EXIT-SUIT/EXIT-SUIT/EXITSUITUnity/Assets/SteamVR/Models/Materials/AlienHand_AlbedoTransparency.png

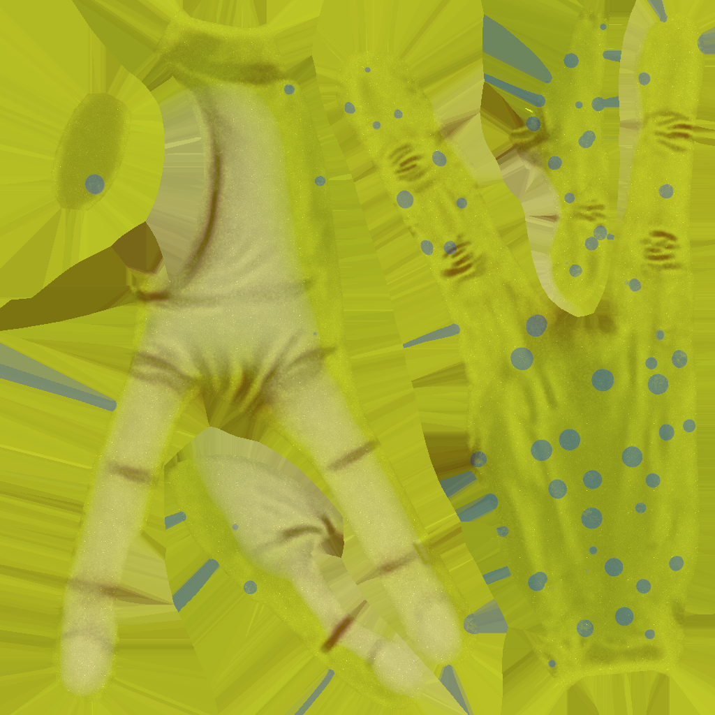
EXITSUITUnity/Assets/SteamVR/Models/Materials/AlienHand_AlbedoTransparency.png
