EXIT-SUIT/EXIT-SUIT/EXITSUITUnity/Assets/SteamVR/InteractionSystem/Samples/Models/Materials/Furniture_Normal.png

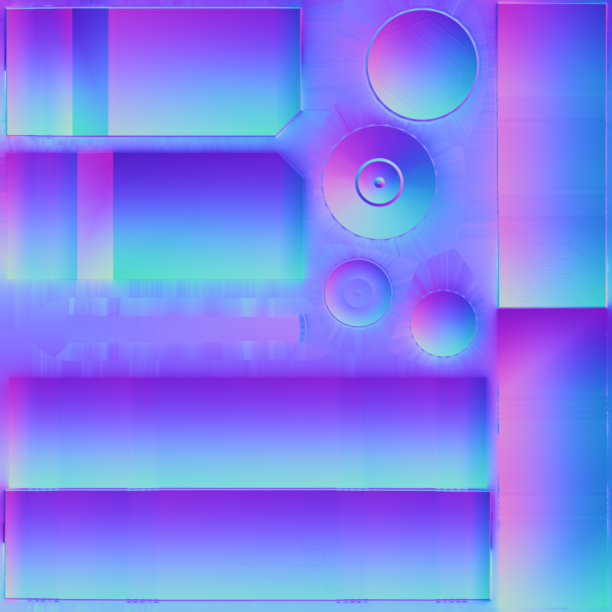
EXITSUITUnity/Assets/SteamVR/InteractionSystem/Samples/Models/Materials/Furniture_Normal.png
