EXIT-SUIT/EXIT-SUIT/EXITSUITUnity/Assets/SteamVR/InteractionSystem/Longbow/Textures/ArcheryWeebleTarget.png

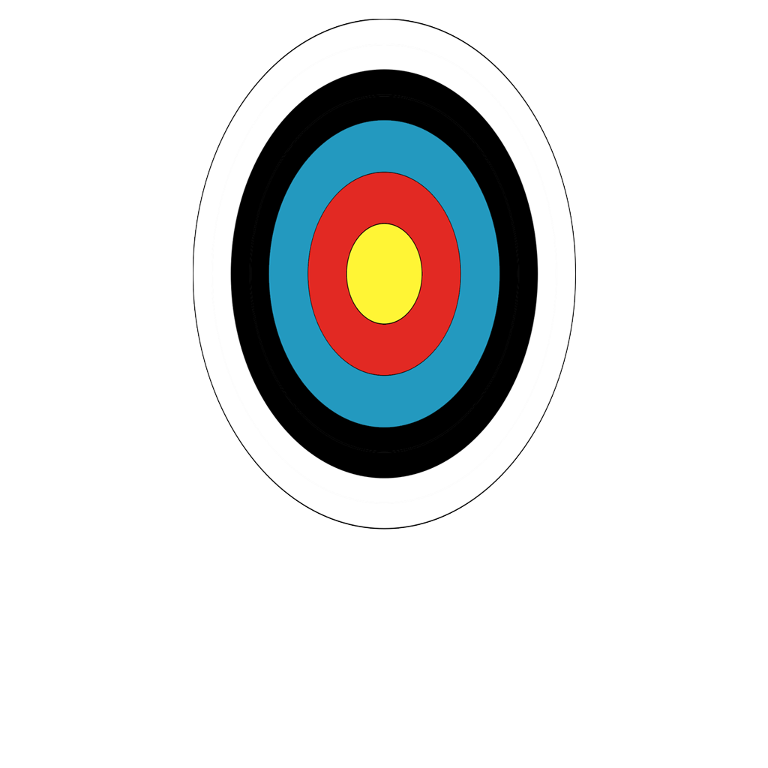
EXITSUITUnity/Assets/SteamVR/InteractionSystem/Longbow/Textures/ArcheryWeebleTarget.png
