EXIT-SUIT/EXIT-SUIT/EXITSUITUnity/Assets/SteamVR/InteractionSystem/Longbow/Textures/ArrowAlbedoTransparency.png

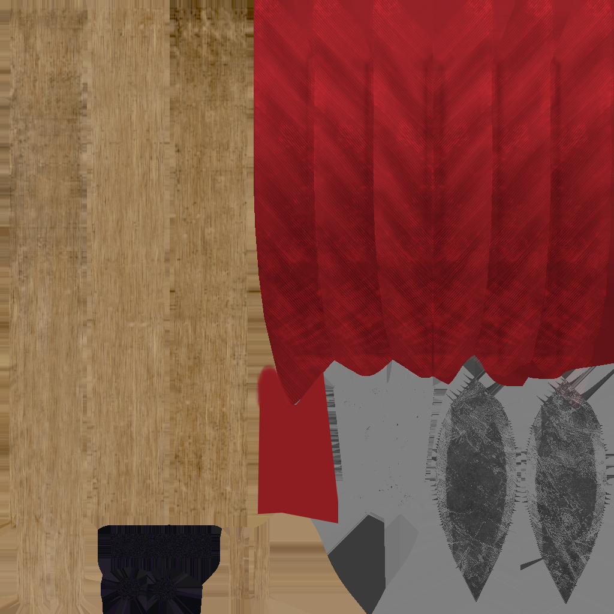
EXITSUITUnity/Assets/SteamVR/InteractionSystem/Longbow/Textures/ArrowAlbedoTransparency.png
