EXIT-SUIT/EXIT-SUIT/EXITSUITUnity/Assets/SteamVR/InteractionSystem/Longbow/Textures/ArrowAmbientOcclusion.png

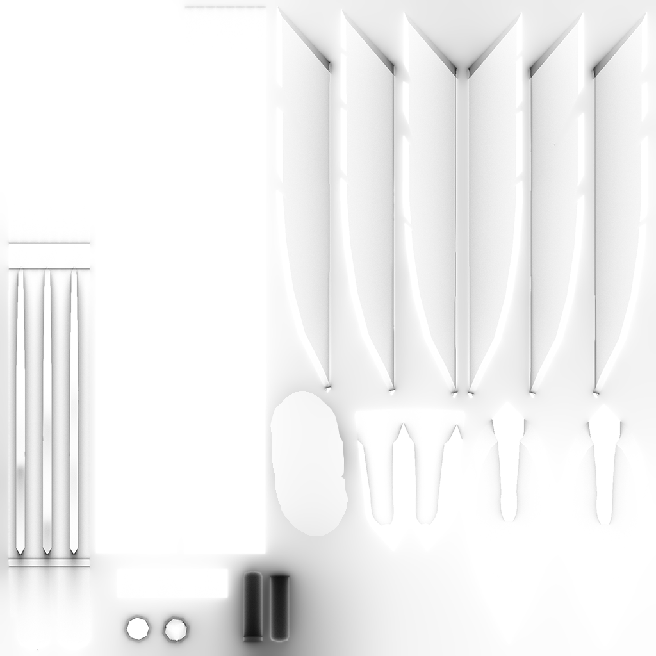
EXITSUITUnity/Assets/SteamVR/InteractionSystem/Longbow/Textures/ArrowAmbientOcclusion.png
