EXIT-SUIT/EXIT-SUIT/EXITSUITUnity/Assets/SteamVR/InteractionSystem/Longbow/Textures/ArrowGlint.png

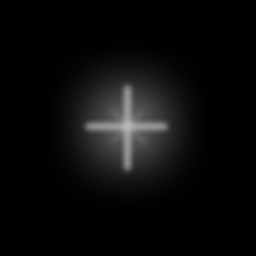
EXITSUITUnity/Assets/SteamVR/InteractionSystem/Longbow/Textures/ArrowGlint.png
