EXIT-SUIT/EXIT-SUIT/EXITSUITUnity/Assets/SteamVR/InteractionSystem/Longbow/Textures/ArrowMetallicSmoothness.png

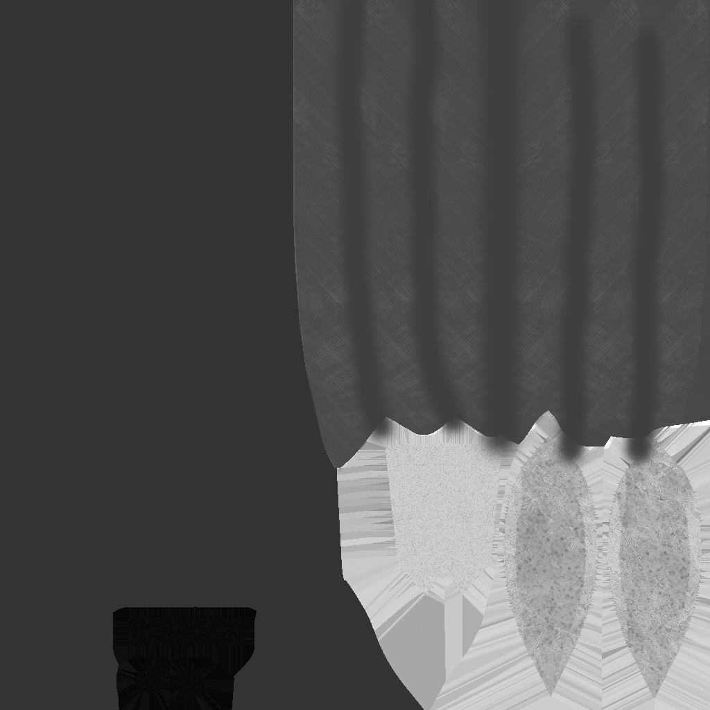
EXITSUITUnity/Assets/SteamVR/InteractionSystem/Longbow/Textures/ArrowMetallicSmoothness.png
