EXIT-SUIT/EXIT-SUIT/EXITSUITUnity/Assets/SteamVR/InteractionSystem/Longbow/Textures/ArrowNormal.png

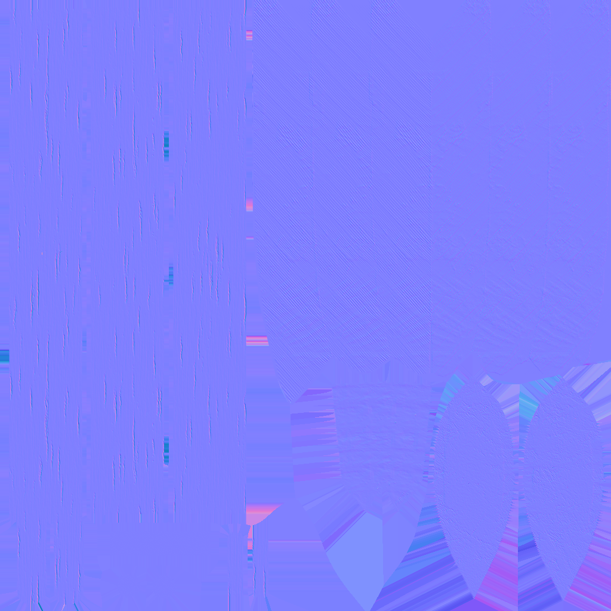
EXITSUITUnity/Assets/SteamVR/InteractionSystem/Longbow/Textures/ArrowNormal.png
