EXIT-SUIT/EXIT-SUIT/EXITSUITUnity/Assets/SteamVR/InteractionSystem/Longbow/Textures/BalloonColor.png

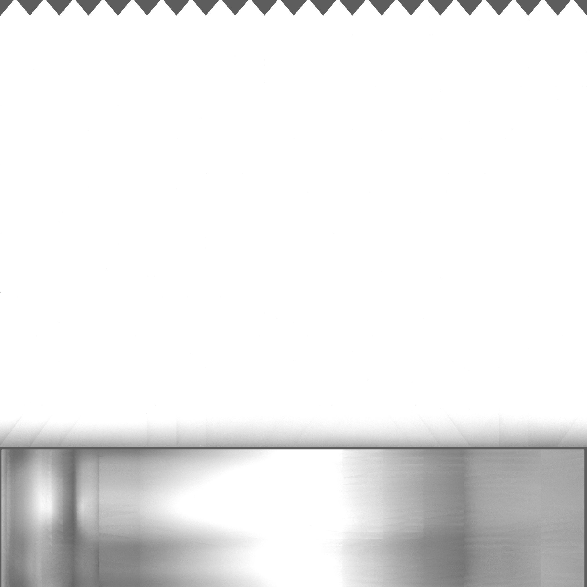
EXITSUITUnity/Assets/SteamVR/InteractionSystem/Longbow/Textures/BalloonColor.png
