EXIT-SUIT/EXIT-SUIT/EXITSUITUnity/Assets/SteamVR/InteractionSystem/Longbow/Textures/Longbow.png

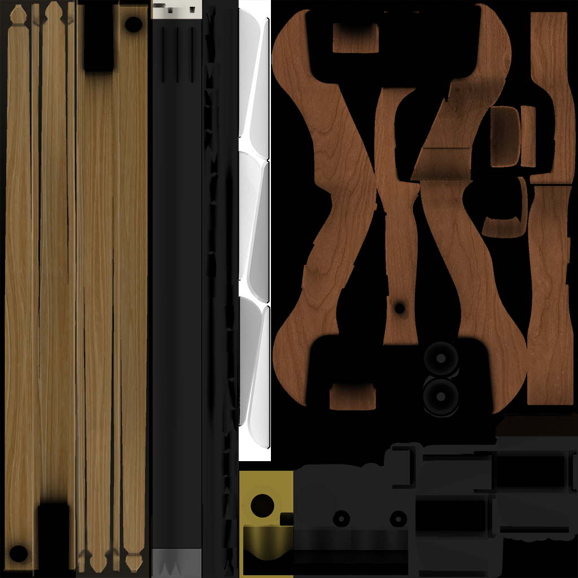
EXITSUITUnity/Assets/SteamVR/InteractionSystem/Longbow/Textures/Longbow.png
