EXIT-SUIT/EXIT-SUIT/EXITSUITUnity/Assets/SteamVR/InteractionSystem/Longbow/Textures/TorchFire.png

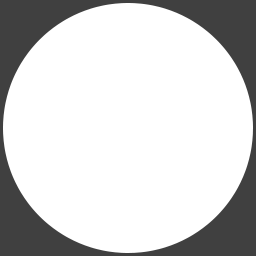
EXITSUITUnity/Assets/SteamVR/InteractionSystem/Longbow/Textures/TorchFire.png
