EXIT-SUIT/EXIT-SUIT/EXITSUITUnity/Assets/SteamVR/InteractionSystem/Samples/Grenade/Nade_Nade_Normal.png

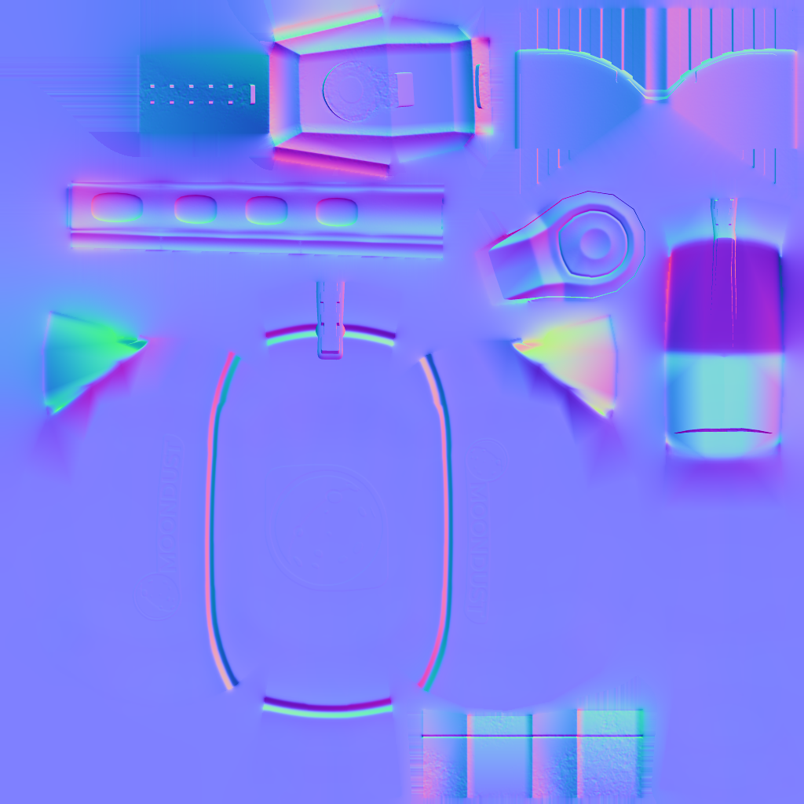
EXITSUITUnity/Assets/SteamVR/InteractionSystem/Samples/Grenade/Nade_Nade_Normal.png
