EXIT-SUIT/EXIT-SUIT/EXITSUITUnity/Assets/SteamVR/InteractionSystem/Samples/Grenade/SunFlare.png

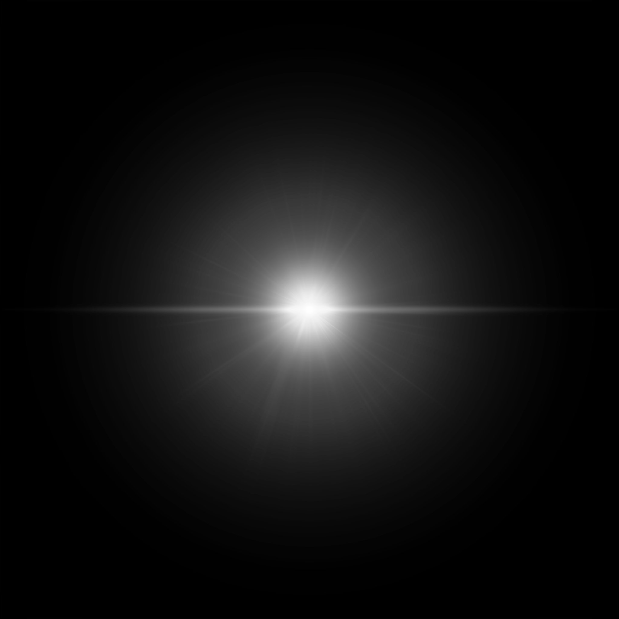
EXITSUITUnity/Assets/SteamVR/InteractionSystem/Samples/Grenade/SunFlare.png
