EXIT-SUIT/EXIT-SUIT/EXITSUITUnity/Assets/SteamVR/InteractionSystem/Samples/Models/black_floor_metal_001a.jpg

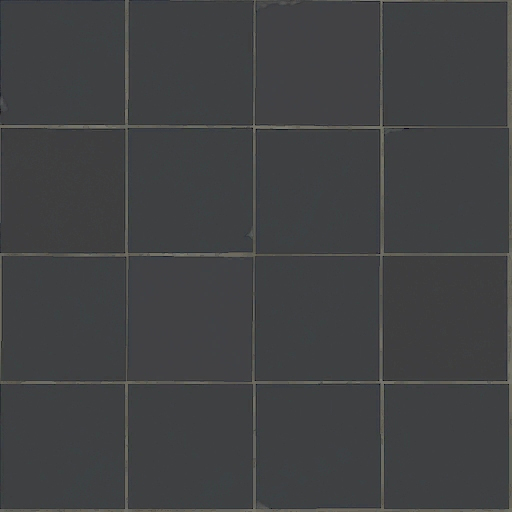
EXITSUITUnity/Assets/SteamVR/InteractionSystem/Samples/Models/black_floor_metal_001a.jpg
