EXIT-SUIT/EXIT-SUIT/EXITSUITUnity/Assets/SteamVR/InteractionSystem/Samples/Models/black_floor_metal_MET.png

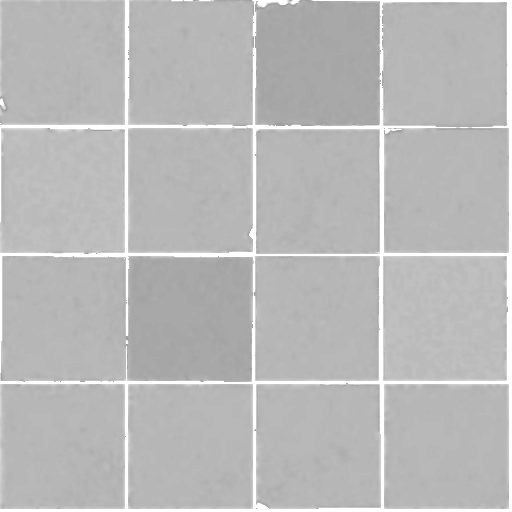
EXITSUITUnity/Assets/SteamVR/InteractionSystem/Samples/Models/black_floor_metal_MET.png
