EXIT-SUIT/EXIT-SUIT/EXITSUITUnity/Assets/SteamVR/InteractionSystem/Samples/Models/black_floor_metal_NRM.jpg

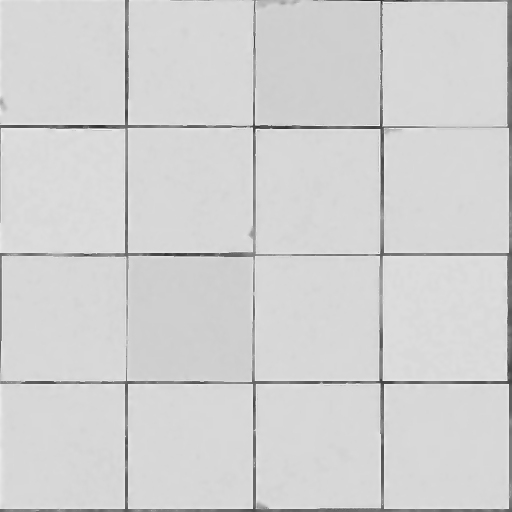
EXITSUITUnity/Assets/SteamVR/InteractionSystem/Samples/Models/black_floor_metal_NRM.jpg
