EXIT-SUIT/EXIT-SUIT/EXITSUITUnity/Assets/SteamVR/InteractionSystem/Samples/Squishy/Textures/gooNoise.png

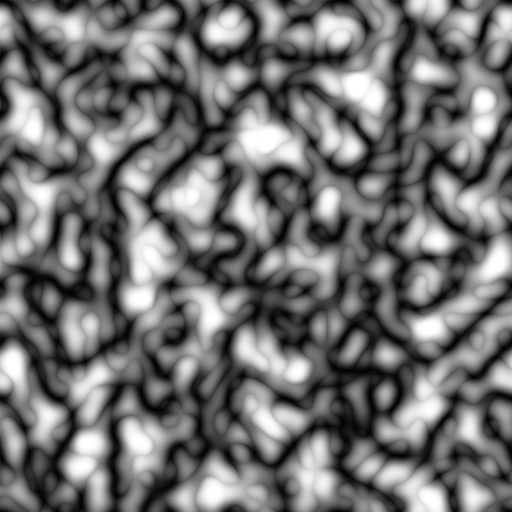
EXITSUITUnity/Assets/SteamVR/InteractionSystem/Samples/Squishy/Textures/gooNoise.png
