EXIT-SUIT/EXIT-SUIT/EXITSUITUnity/Assets/SteamVR/InteractionSystem/Samples/Squishy/Textures/gooNrm.png

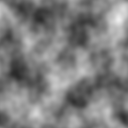
EXITSUITUnity/Assets/SteamVR/InteractionSystem/Samples/Squishy/Textures/gooNrm.png
