EXIT-SUIT/EXIT-SUIT/EXITSUITUnity/Assets/SteamVR/InteractionSystem/Samples/Textures/estimatedOnHand.png

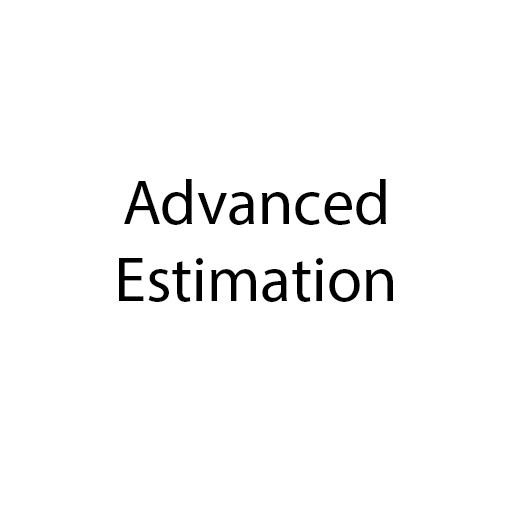
EXITSUITUnity/Assets/SteamVR/InteractionSystem/Samples/Textures/estimatedOnHand.png
