EXIT-SUIT/EXIT-SUIT/EXITSUITUnity/Assets/SteamVR/InteractionSystem/Samples/Textures/estimatedOnObject.png

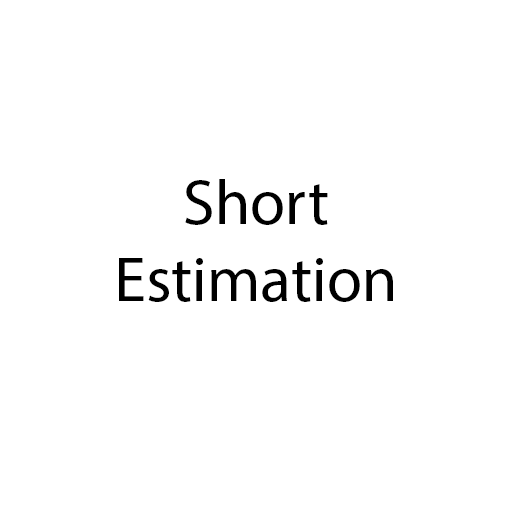
EXITSUITUnity/Assets/SteamVR/InteractionSystem/Samples/Textures/estimatedOnObject.png
