EXIT-SUIT/EXIT-SUIT/EXITSUITUnity/Assets/SteamVR/InteractionSystem/Samples/Textures/fabric nrm.png

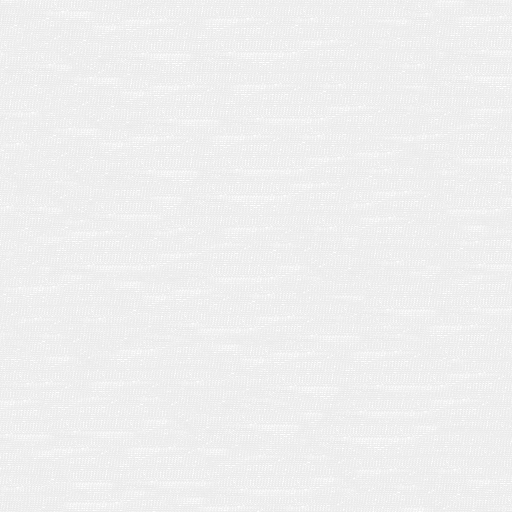
EXITSUITUnity/Assets/SteamVR/InteractionSystem/Samples/Textures/fabric nrm.png
