EXIT-SUIT/EXIT-SUIT/EXITSUITUnity/Assets/SteamVR/InteractionSystem/Samples/Textures/TargetLO_target_Normal.png

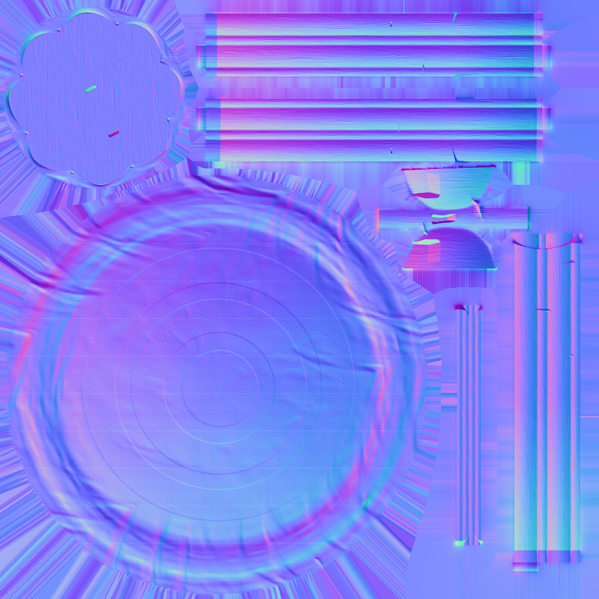
EXITSUITUnity/Assets/SteamVR/InteractionSystem/Samples/Textures/TargetLO_target_Normal.png
