EXIT-SUIT/EXIT-SUIT/EXITSUITUnity/Assets/SteamVR/Textures/background.png

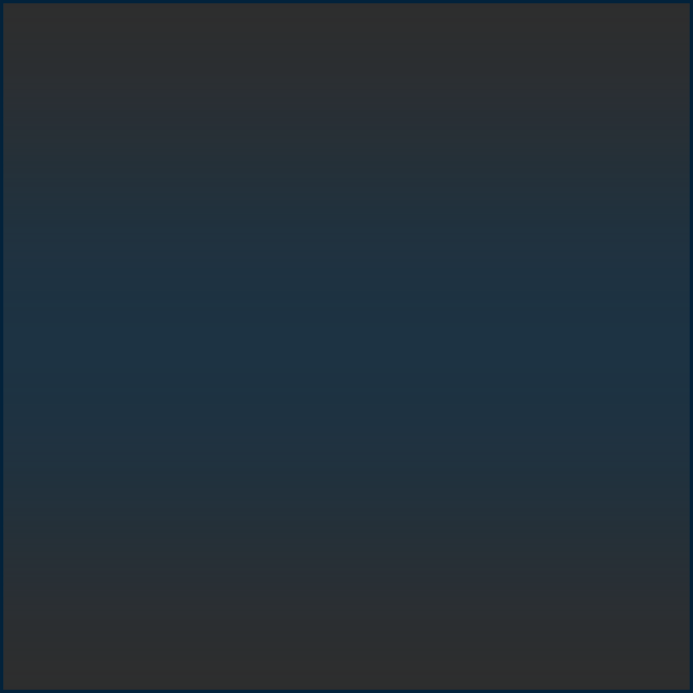
EXITSUITUnity/Assets/SteamVR/Textures/background.png
