EXIT-SUIT/EXIT-SUIT/EXITSUITUnity/Assets/SteamVR/Textures/workshop.png

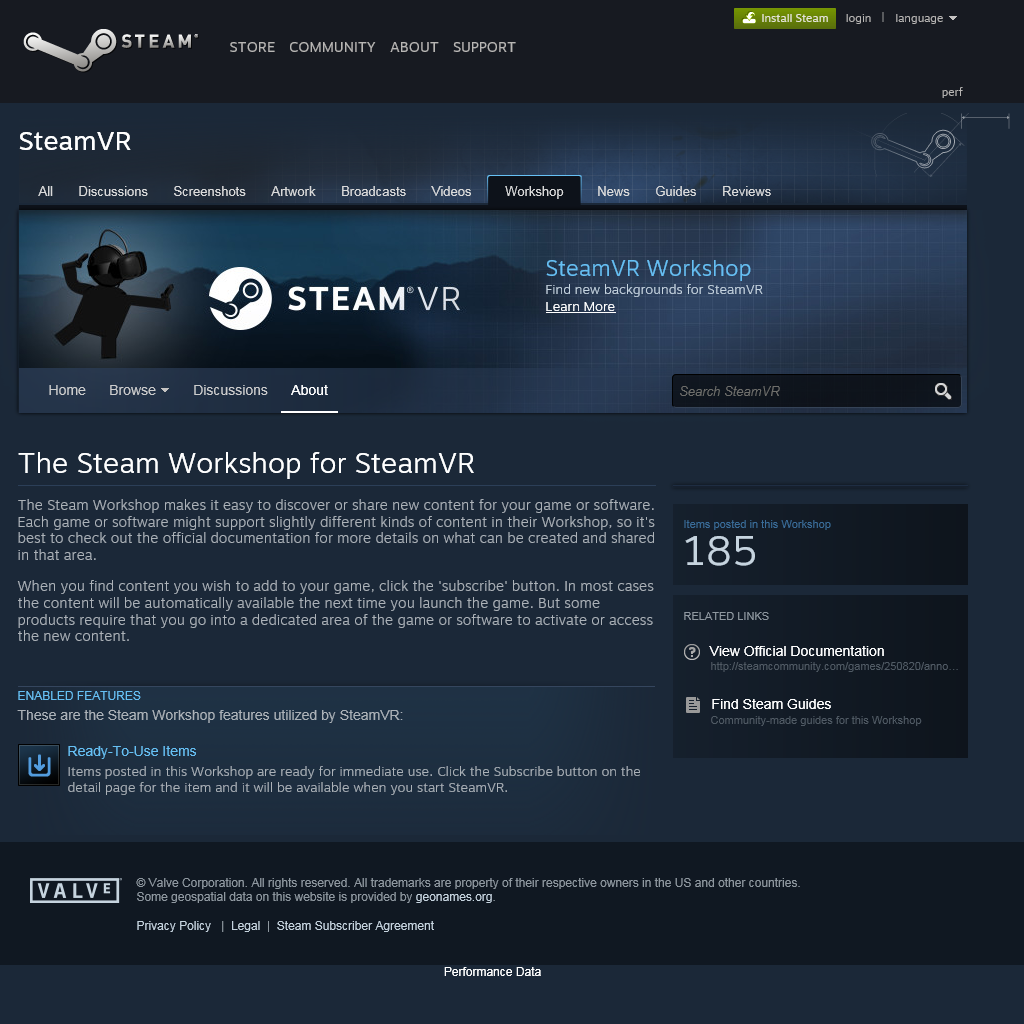
EXITSUITUnity/Assets/SteamVR/Textures/workshop.png
