EXIT-SUIT/EXIT-SUIT/EXITSUITUnity/Assets/SteamVR/Models/Materials/AlienHand_MetallicSmoothness.png

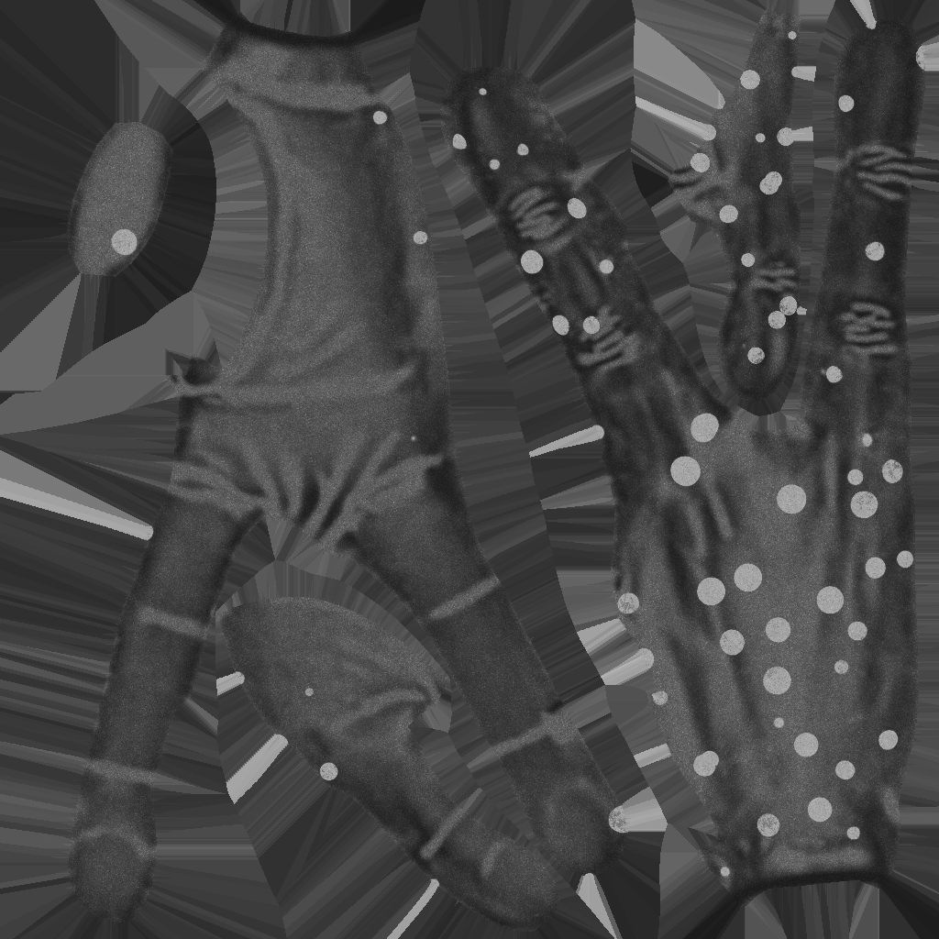
EXITSUITUnity/Assets/SteamVR/Models/Materials/AlienHand_MetallicSmoothness.png
