EXIT-SUIT/EXIT-SUIT/EXITSUITUnity/Assets/SteamVR/Models/Materials/AlienHand_Normal.png

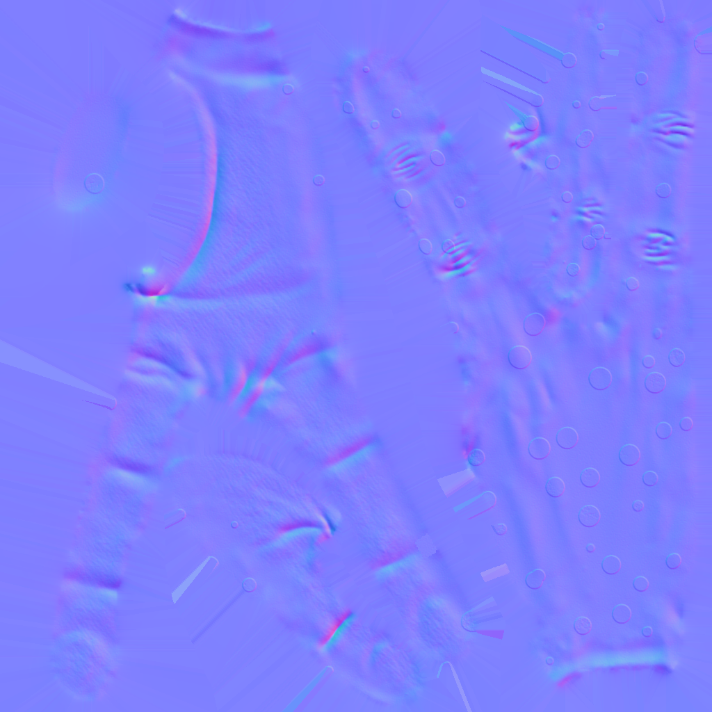
EXITSUITUnity/Assets/SteamVR/Models/Materials/AlienHand_Normal.png
