EXIT-SUIT/EXIT-SUIT/EXITSUITUnity/Assets/SteamVR/Models/Materials/floppyHand Emit.png

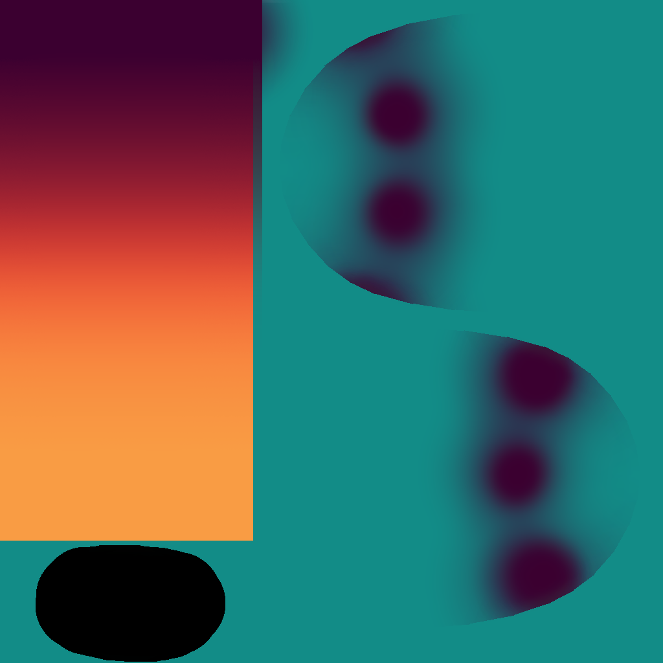
EXITSUITUnity/Assets/SteamVR/Models/Materials/floppyHand Emit.png
