EXIT-SUIT/EXIT-SUIT/EXITSUITUnity/Assets/SteamVR/Models/Materials/vr_glove_color_red.jpg

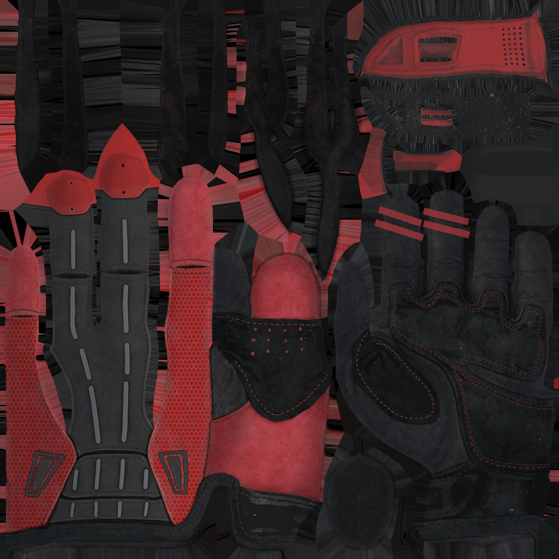
EXITSUITUnity/Assets/SteamVR/Models/Materials/vr_glove_color_red.jpg
