EXIT-SUIT/EXIT-SUIT/EXITSUITUnity/Assets/SteamVR/Models/Materials/vr_glove_normal.png

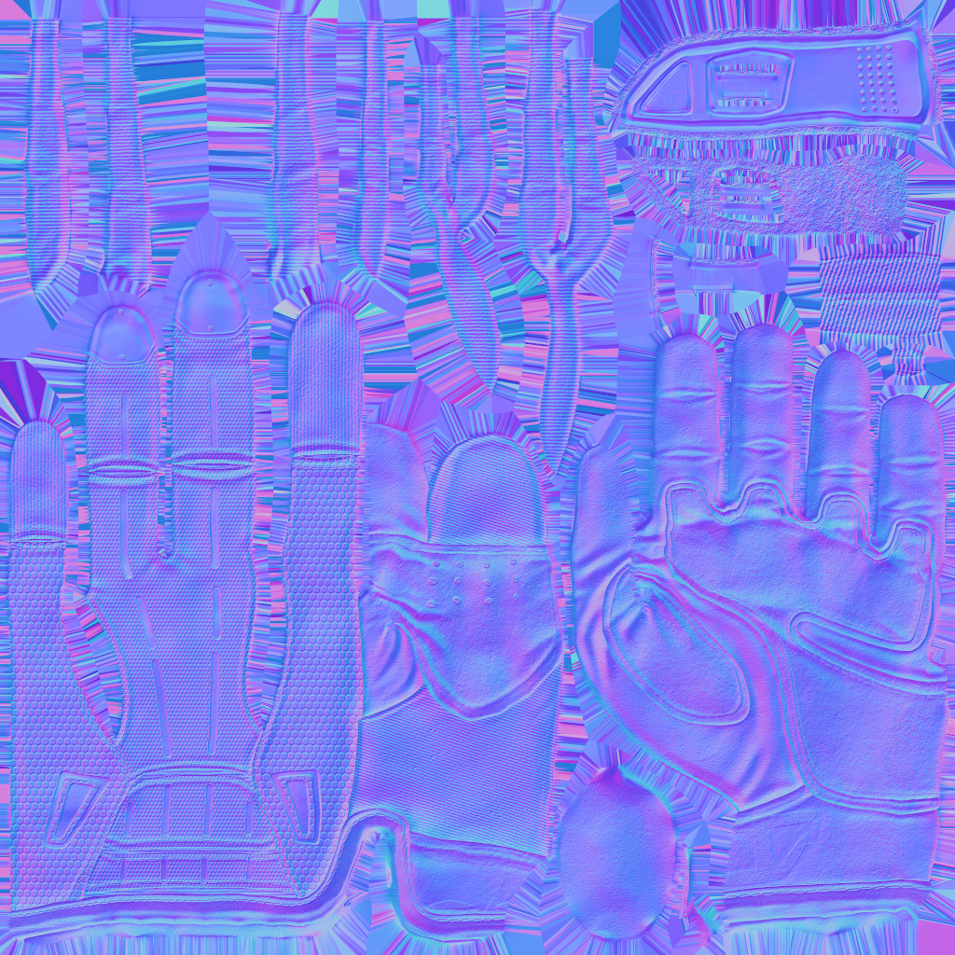
EXITSUITUnity/Assets/SteamVR/Models/Materials/vr_glove_normal.png
